mark1791/Acorn_Plus_1_Reimagine/Images/IMG_9799.jpg

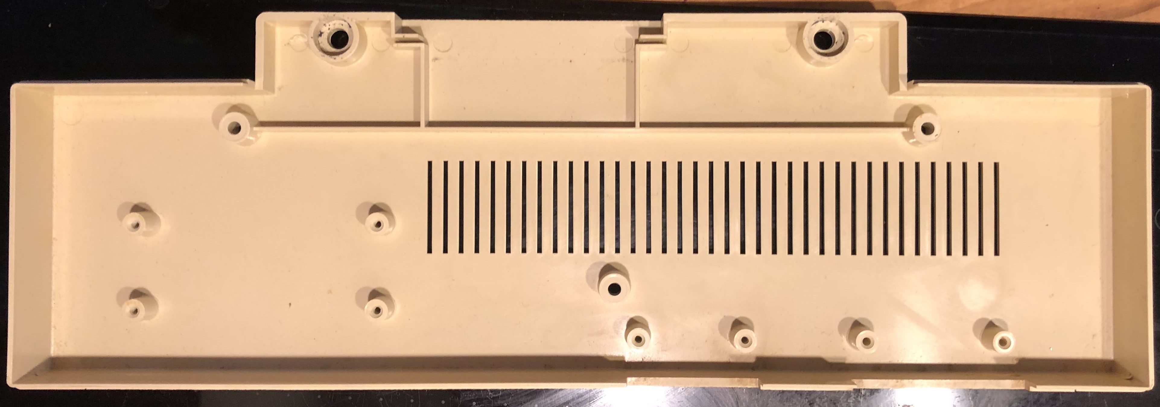
Images/IMG_9799.jpg
