mark1791/Acorn_Plus_1_Reimagine/Images/IMG_9800.jpg

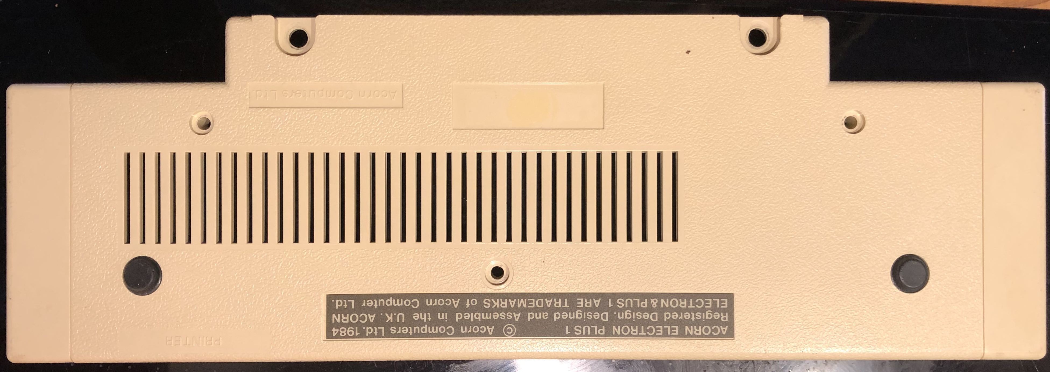
Images/IMG_9800.jpg
