mark1791/Acorn_Plus_1_Reimagine/Images/IMG_9804.jpg

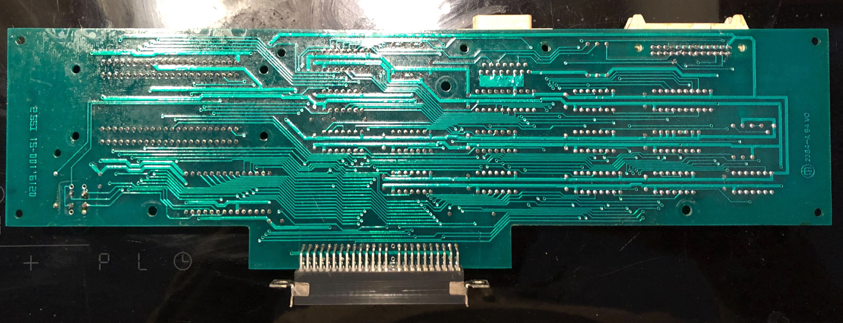
Images/IMG_9804.jpg
