mark1791/Acorn_Plus_1_Reimagine/001-Acorn-Electron-Plus1-GitHub/001-Acorn-Electron-Plus1.kicad_sch

## KiCad design 001-Acorn-Electron-Plus1-GitHub/001-Acorn-Electron-Plus1.kicad_sch (2023-06-26)

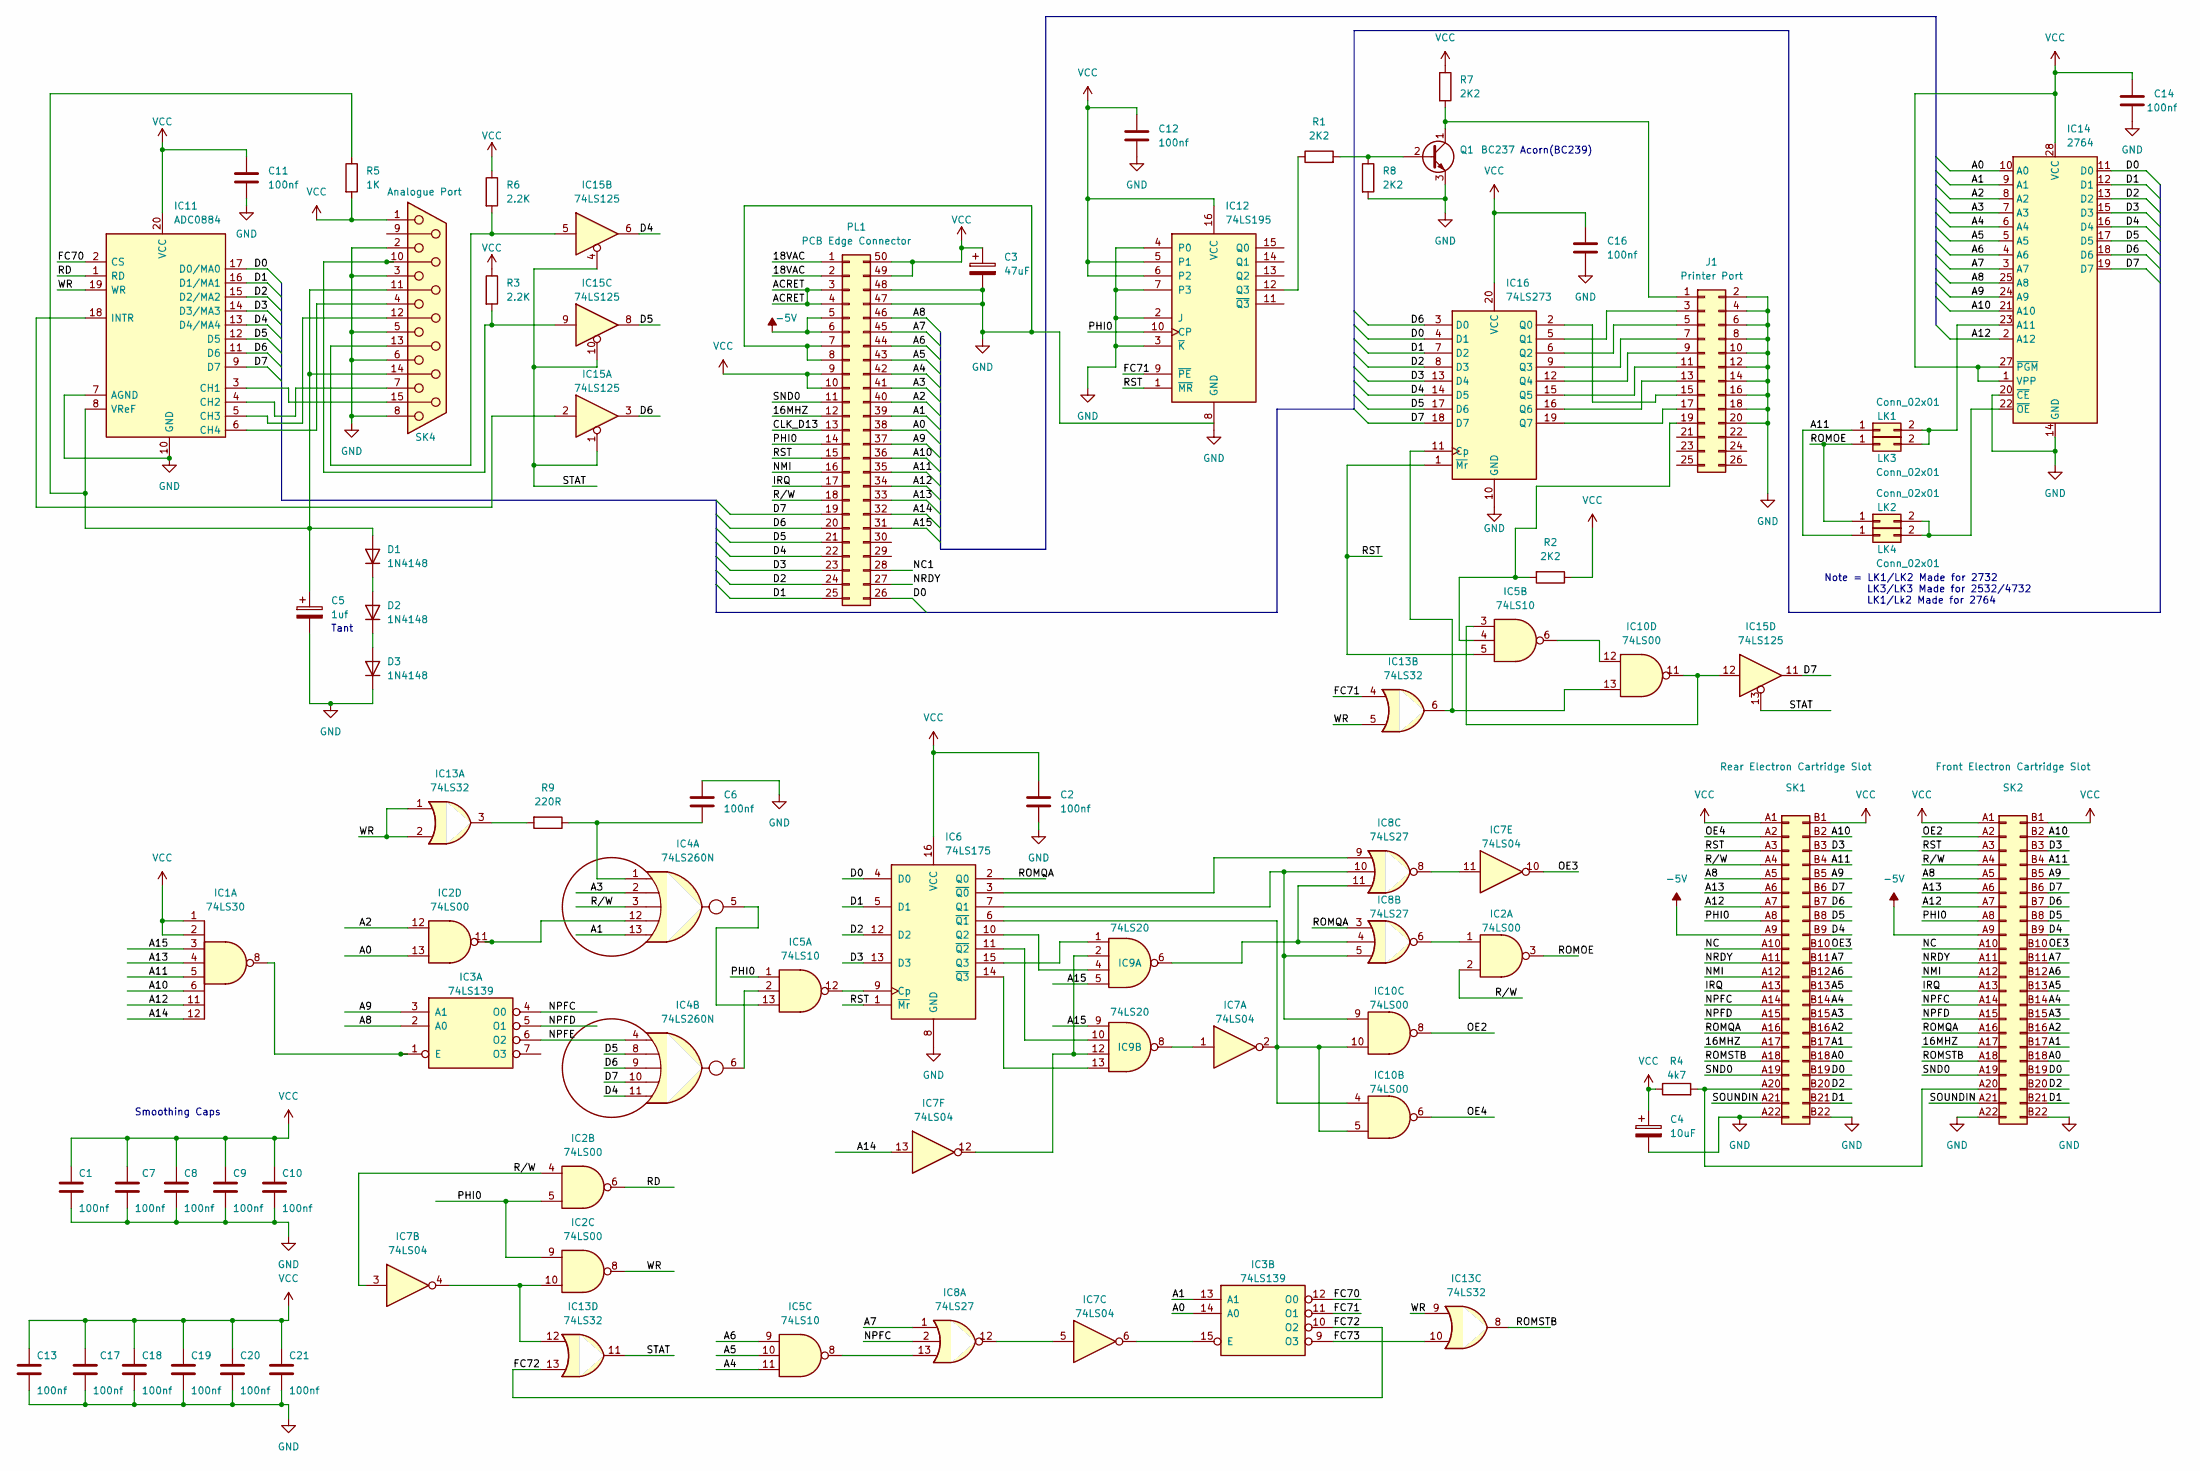
[picture p13: schematic 001-Acorn-Electron-Plus1.kicad_sch]

Parts:
C1, C13: 100nf; C_Disc_D7.0mm_W2.5mm_P5.00mm
C2, C7, C8, C9, C10, C11, C12, C14, C16, C17, C18, C19, C20, C21: 100nf; C_Disc_D6.0mm_W2.5mm_P5.00mm
C3: 47uF; CP_Axial_L11.0mm_D6.0mm_P18.00mm_Horizontal
C4: 10uF; CP_Radial_Tantal_D5.5mm_P5.00mm
C5: 1uf; CP_Radial_Tantal_D6.0mm_P5.00mm
C6: 100nf; CP_Radial_Tantal_D6.0mm_P5.00mm
D1, D2, D3: 1N4148; D_DO-35_SOD27_P7.62mm_Horizontal
IC1: 74LS30; DIP-14_W7.62mm
IC2, IC10: 74LS00; DIP-14_W7.62mm
IC3: 74LS139; DIP-16_W7.62mm
IC4: 74LS260N; DIP-14_W7.62mm
IC5: 74LS10; DIP-14_W7.62mm
IC6: 74LS175; DIP-16_W7.62mm
IC7: 74LS04; DIP-14_W7.62mm
IC8: 74LS27; DIP-14_W7.62mm
IC9: 74LS20; DIP-14_W7.62mm
IC11: ADC0884; DIP-20_W7.62mm
IC12: 74LS195; DIP-16_W7.62mm
IC13: 74LS32; DIP-14_W7.62mm
IC14: 2764; DIP-28_W15.24mm
IC15: 74LS125; DIP-14_W7.62mm
IC16: 74LS273; DIP-20_W7.62mm
J1: Printer Port; IDC-Header_2x13_P2.54mm_Latch_Horizontal
LK1, LK2, LK3, LK4: Conn_02x01; PinHeader_1x02_P2.54mm_Vertical
PL1: PCB Edge Connector; acorn_electron_48pin_expansion_connector
Q1: BC237; TO-92_Inline
R1, R2, R7, R8: 2K2; R_Axial_DIN0207_L6.3mm_D2.5mm_P7.62mm_Horizontal
R3, R6: 2.2K; R_Axial_DIN0207_L6.3mm_D2.5mm_P7.62mm_Horizontal
R4: 4k7; R_Axial_DIN0207_L6.3mm_D2.5mm_P7.62mm_Horizontal
R5: 1K; R_Axial_DIN0207_L6.3mm_D2.5mm_P7.62mm_Horizontal
R9: 220R; R_Axial_DIN0207_L6.3mm_D2.5mm_P7.62mm_Horizontal
SK1: Rear Electron Cartridge Slot; acorn_electron_cartridge_socket
SK2: Front Electron Cartridge Slot; acorn_electron_cartridge_socket
SK4: Analogue Port; DSUB-15_Female_Horizontal_P2.77x2.54mm_EdgePinOffset9.40mm

Connections:
16MHZ: PL1.12, SK1.A17 (Pin_a17), SK2.A17 (Pin_a17)
18VAC: PL1.1, PL1.2
-5V: PL1.5, PL1.6, SK1.A9 (Pin_a9), SK2.A9 (Pin_a9)
A0: IC2.13, IC3.14 (A0), IC14.10 (A0), PL1.38, SK1.B18 (Pin_b18), SK2.B18 (Pin_b18)
A1: IC3.13 (A1), IC4.13, IC14.9 (A1), PL1.39, SK1.B17 (Pin_b17), SK2.B17 (Pin_b17)
A2: IC2.12, IC14.8 (A2), PL1.40, SK1.B16 (Pin_b16), SK2.B16 (Pin_b16)
A3: IC4.2, IC14.7 (A3), PL1.41, SK1.B15 (Pin_b15), SK2.B15 (Pin_b15)
A4: IC5.11, IC14.6 (A4), PL1.42, SK1.B14 (Pin_b14), SK2.B14 (Pin_b14)
A5: IC5.10, IC14.5 (A5), PL1.43, SK1.B13 (Pin_b13), SK2.B13 (Pin_b13)
A6: IC5.9, IC14.4 (A6), PL1.44, SK1.B12 (Pin_b12), SK2.B12 (Pin_b12)
A7: IC8.1, IC14.3 (A7), PL1.45, SK1.B11 (Pin_b11), SK2.B11 (Pin_b11)
A8: IC3.2 (A0), IC14.25 (A8), PL1.46, SK1.A5 (Pin_a5), SK2.A5 (Pin_a5)
A9: IC3.3 (A1), IC14.24 (A9), PL1.37, SK1.B5, SK2.B5
A10: IC1.6, IC14.21 (A10), PL1.36, SK1.B2 (Pin_b2), SK2.B2 (Pin_b2)
A11: IC1.5, LK1.1, LK4.1, PL1.35, SK1.B4 (Pin_b4), SK2.B4 (Pin_b4)
A12: IC1.11, IC14.2 (A12), PL1.34, SK1.A7 (Pin_a7), SK2.A7 (Pin_a7)
A13: IC1.4, PL1.33, SK1.A6 (Pin_a6), SK2.A6 (Pin_a6)
A14: IC1.12, IC7.13, PL1.32
A15: IC1.3, IC9.5, IC9.9, PL1.31
ACRET: PL1.3, PL1.4
CLK_D13: PL1.13
D0: IC6.4 (D0), IC11.17 (D0/MA0), IC14.11 (D0), IC16.4 (D1), PL1.26, SK1.B19 (Pin_b19), SK2.B19 (Pin_b19)
D1: IC6.5 (D1), IC11.16 (D1/MA1), IC14.12 (D1), IC16.7 (D2), PL1.25, SK1.B21 (Pin_b21), SK2.B21 (Pin_b21)
D2: IC6.12 (D2), IC11.15 (D2/MA2), IC14.13 (D2), IC16.8 (D3), PL1.24, SK1.B20 (Pin_b20), SK2.B20 (Pin_b20)
D3: IC6.13 (D3), IC11.14 (D3/MA3), IC14.15 (D3), IC16.13 (D4), PL1.23, SK1.B3 (Pin_b3), SK2.B3 (Pin_b3)
D4: IC4.11, IC11.13 (D4/MA4), IC14.16 (D4), IC15.6, IC16.14 (D5), PL1.22, SK1.B9 (Pin_b9), SK2.B9 (Pin_b9)
D5: IC4.8, IC11.12 (D5), IC14.17 (D5), IC15.8, IC16.17 (D6), PL1.21, SK1.B8 (Pin_b8), SK2.B8 (Pin_b8)
D6: IC4.9, IC11.11 (D6), IC14.18 (D6), IC15.3, IC16.3 (D0), PL1.20, SK1.B7 (Pin_b7), SK2.B7 (Pin_b7)
D7: IC4.10, IC11.9 (D7), IC14.19 (D7), IC15.11, IC16.18 (D7), PL1.19, SK1.B6 (Pin_b6), SK2.B6 (Pin_b6)
FC70: IC3.12 (O0), IC11.2 (CS)
FC71: IC3.11 (O1), IC12.9 (~PE), IC13.4
FC72: IC3.10 (O2), IC13.13
FC73: IC3.9 (O3), IC13.10
GND: C1.2, C2.2, C3.2, C4.2, C5.2, C6.1, C7.2, C8.2, C9.2, C10.2, C11.2, C12.2, C13.2, C14.2, C16.2, C17.2, C18.2, C19.2, C20.2, C21.2, D3.1 (K), IC6.8 (GND), IC11.7 (AGND), IC11.10 (GND), IC12.2 (J), IC12.3 (~K), IC12.4 (P0), IC12.7 (P3), IC12.8 (GND), IC14.14 (GND), IC14.20 (~CE), IC16.10 (GND), J1.2, J1.4, J1.6, J1.8, J1.10, J1.12, J1.14, J1.16, J1.18, J1.20, PL1.7, PL1.8, PL1.47, PL1.48, Q1.3 (E), R8.2, SK1.A22 (Pin_a22), SK1.B22, SK2.A22 (Pin_a22), SK2.B22, SK4.2, SK4.3, SK4.5, SK4.6, SK4.8
IRQ: PL1.17, SK1.A13 (Pin_a13), SK2.A13 (Pin_a13)
NC: SK1.A10 (Pin_a10), SK2.A10 (Pin_a10)
NC1: PL1.28
NMI: PL1.16, SK1.A12 (Pin_a12), SK2.A12 (Pin_a12)
NPFC: IC3.4 (O0), IC8.2, SK1.A14 (Pin_a14), SK2.A14 (Pin_a14)
NPFD: IC3.5 (O1), SK1.A15 (Pin_a15), SK2.A15 (Pin_a15)
NPFE: IC3.6 (O2), IC4.4
NRDY: PL1.27, SK1.A11 (Pin_a11), SK2.A11 (Pin_a11)
unnamed: C5.1, D1.2 (A), IC11.8 (VReF), R5.1, SK4.11 (P111), SK4.14
unnamed: C6.2, IC4.1, R9.1
unnamed: D1.1 (K), D2.2 (A)
unnamed: D2.1 (K), D3.2 (A)
unnamed: IC1.8, IC3.1 (E)
unnamed: IC2.1, IC8.6
unnamed: IC2.11, IC4.12
unnamed: IC3.15 (E), IC7.6
unnamed: IC4.5, IC5.13
unnamed: IC4.6, IC5.2
unnamed: IC5.4, J1.19, R2.2
unnamed: IC5.8, IC8.13
unnamed: IC5.12, IC6.9 (Cp)
unnamed: IC6.3 (~Q0), IC8.9
unnamed: IC6.10 (Q2), IC9.4
unnamed: IC6.11 (~Q2), IC9.10
unnamed: IC6.14 (~Q3), IC9.13
unnamed: IC6.15 (Q3), IC9.1
unnamed: IC7.1, IC9.8
unnamed: IC7.5, IC8.12
unnamed: IC7.11, IC8.8
unnamed: IC7.12, IC9.2, IC9.12
unnamed: IC8.4, IC8.11, IC9.6
unnamed: IC6.7 (Q1), IC8.5, IC8.10, IC10.9
unnamed: IC6.6 (~Q1), IC7.2, IC10.4, IC10.5, IC10.10
unnamed: IC5.3, IC10.11, IC15.12
unnamed: IC5.6, IC10.12
unnamed: IC10.13, IC13.6, IC16.11 (Cp)
unnamed: IC11.3 (CH1), SK4.15
unnamed: IC11.4 (CH2), SK4.7
unnamed: IC11.5 (CH3), SK4.12
unnamed: IC11.6 (CH4), SK4.4
unnamed: IC11.18 (INTR), IC15.2
unnamed: IC12.12 (Q3), R1.1
unnamed: IC13.3, R9.2
unnamed: IC2.10, IC7.4, IC13.12
unnamed: IC14.22 (~OE), LK2.2, LK4.2
unnamed: IC14.23 (A11), LK1.2, LK3.2
unnamed: IC15.5, R6.2, SK4.13
unnamed: IC15.9, R3.2, SK4.10
unnamed: IC16.2 (Q0), J1.15
unnamed: IC16.5 (Q1), J1.3
unnamed: IC16.6 (Q2), J1.5
unnamed: IC16.9 (Q3), J1.7
unnamed: IC16.12 (Q4), J1.9
unnamed: IC16.15 (Q5), J1.11
unnamed: IC16.16 (Q6), J1.13
unnamed: IC16.19 (Q7), J1.17
unnamed: J1.1, Q1.1 (C), R7.2
unnamed: Q1.2 (B), R1.2, R8.1
unnamed: R4.2, SK1.A20 (Pin_a20), SK2.A20 (Pin_a20)
OE2: IC10.8, SK2.A2 (Pin_a2)
OE3: IC7.10, SK1.B10 (Pin_b10), SK2.B10 (Pin_b10)
OE4: IC10.6, SK1.A2 (Pin_a2)
PHI0: IC2.5, IC2.9, IC5.1, IC12.10 (CP), PL1.14, SK1.A8 (Pin_a8), SK2.A8 (Pin_a8)
RD: IC2.6, IC11.1 (RD)
ROMOE: IC2.3, LK2.1, LK3.1
ROMQA: IC6.2 (Q0), IC8.3, SK1.A16 (Pin_a16), SK2.A16 (Pin_a16)
ROMSTB: IC13.8, SK1.A18 (Pin_a18), SK2.A18 (Pin_a18)
RST: IC5.5, IC6.1 (~Mr), IC12.1 (~MR), IC16.1 (~Mr), PL1.15, SK1.A3 (Pin_a3), SK2.A3 (Pin_a3)
R/W: IC2.2, IC2.4, IC4.3, IC7.3, PL1.18, SK1.A4 (Pin_a4), SK2.A4 (Pin_a4)
SND0: PL1.11, SK1.A19 (Pin_a19), SK2.A19 (Pin_a19)
SOUNDIN: SK1.A21 (Pin_a21), SK2.A21 (Pin_a21)
STAT: IC13.11, IC15.1, IC15.4, IC15.10, IC15.13
VCC: C1.1, C2.1, C3.1, C4.1, C7.1, C8.1, C9.1, C10.1, C11.1, C12.1, C13.1, C14.1, C16.1, C17.1, C18.1, C19.1, C20.1, C21.1, IC1.1, IC1.2, IC6.16 (VCC), IC11.20 (VCC), IC12.5 (P1), IC12.6 (P2), IC12.16 (VCC), IC14.1 (VPP), IC14.27 (~PGM), IC14.28 (VCC), IC16.20 (VCC), PL1.9, PL1.10, PL1.49, PL1.50, R2.1, R3.1, R4.1, R5.2, R6.1, R7.1, SK1.A1 (Pin_a1), SK1.B1 (Pin_b1), SK2.A1 (Pin_a1), SK2.B1 (Pin_b1), SK4.1
WR: IC2.8, IC11.19 (WR), IC13.1, IC13.2, IC13.5, IC13.9

Notes on the sheet:
Note = LK1/LK2 Made for 2732 LK3/LK3 Made for 2532/4732 LK1/Lk2 Made for 2764
Tant
Acorn(BC239)
Smoothing Caps
